McNugget6750/K40-grbl-board/pictures/IMG_8582.JPG

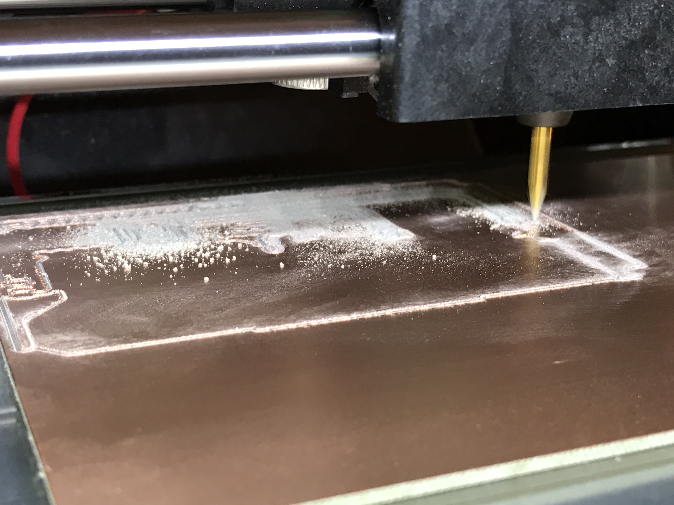
pictures/IMG_8582.JPG
