McNugget6750/K40-grbl-board/pictures/IMG_8585.JPG

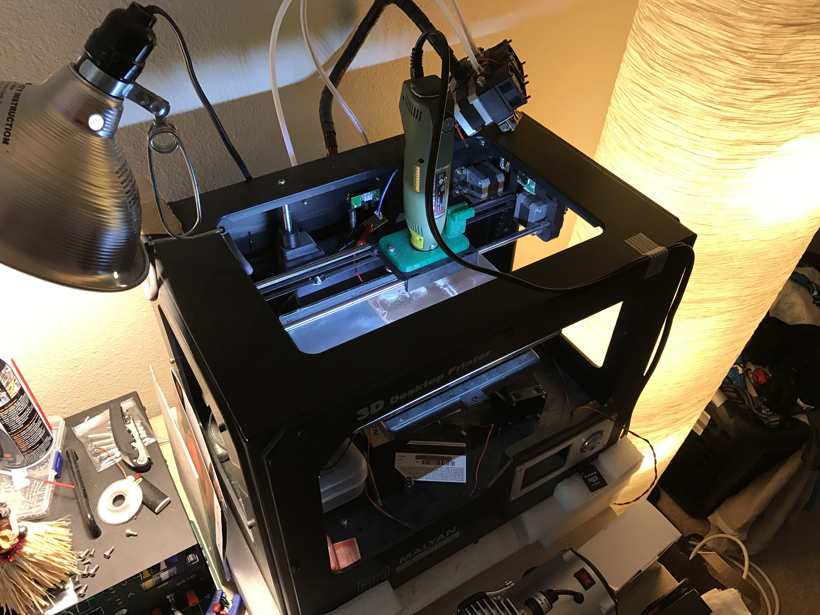
pictures/IMG_8585.JPG
