McNugget6750/K40-grbl-board/pictures/IMG_8590.JPG

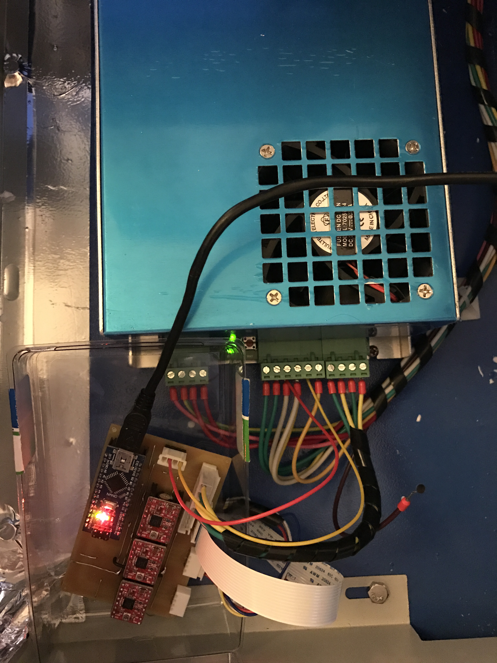
pictures/IMG_8590.JPG
